jedashford/dark-moth-site/preview/board.png

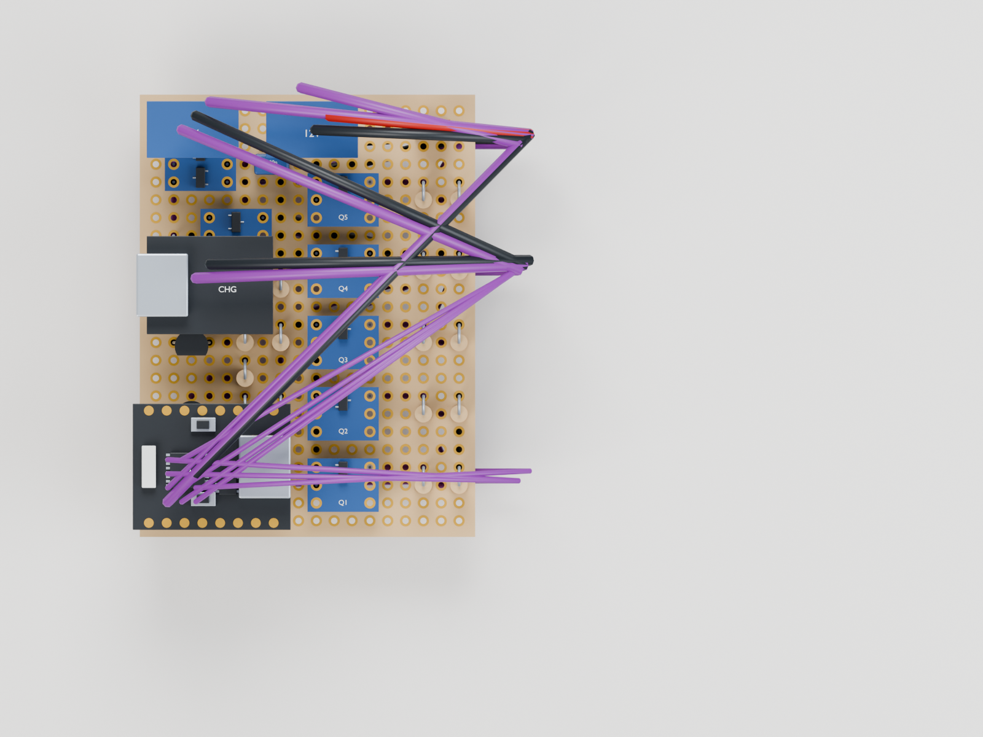
preview/board.png
