jedashford/dark-moth-site/preview/internals.png

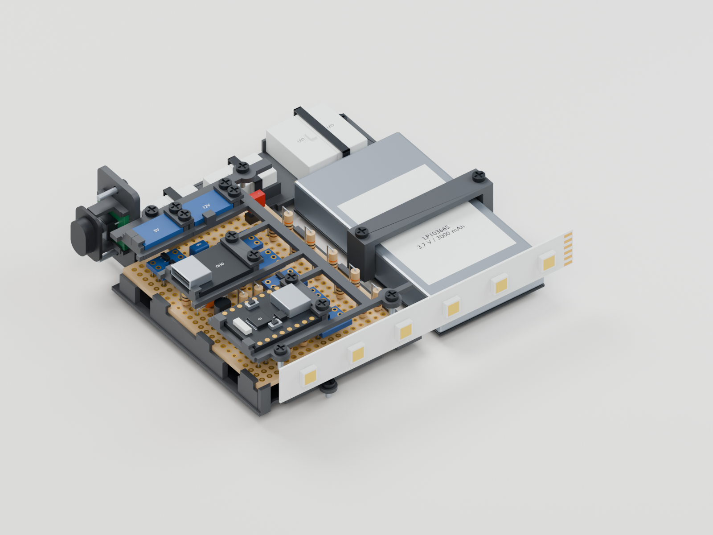
preview/internals.png
