jedashford/dark-moth-site/preview/side.png

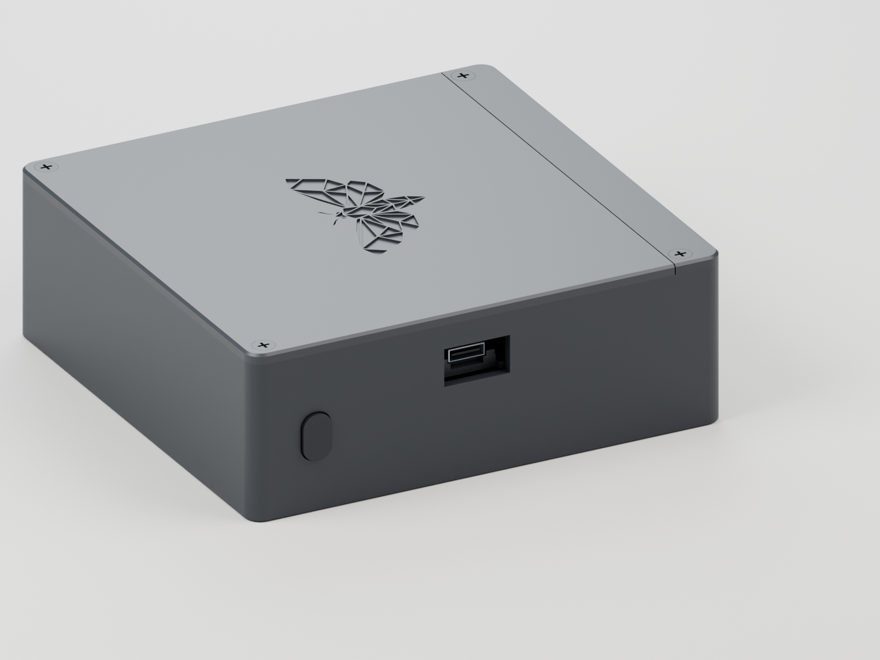
preview/side.png
