jedashford/dark-moth-site/preview/site/perfboard/carrier-angle.png

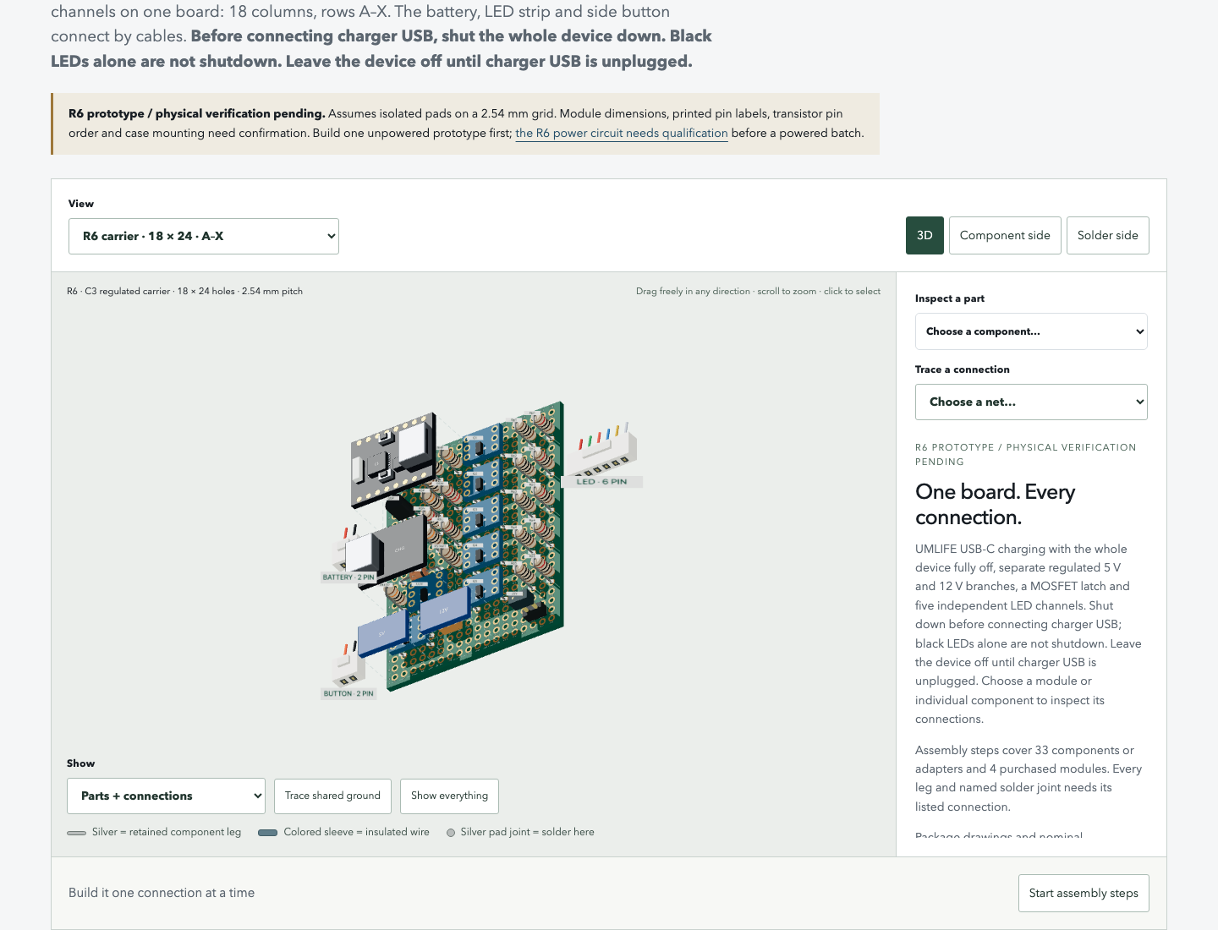
preview/site/perfboard/carrier-angle.png
