jedashford/dark-moth-site/preview/site/perfboard/carrier-bottom.png

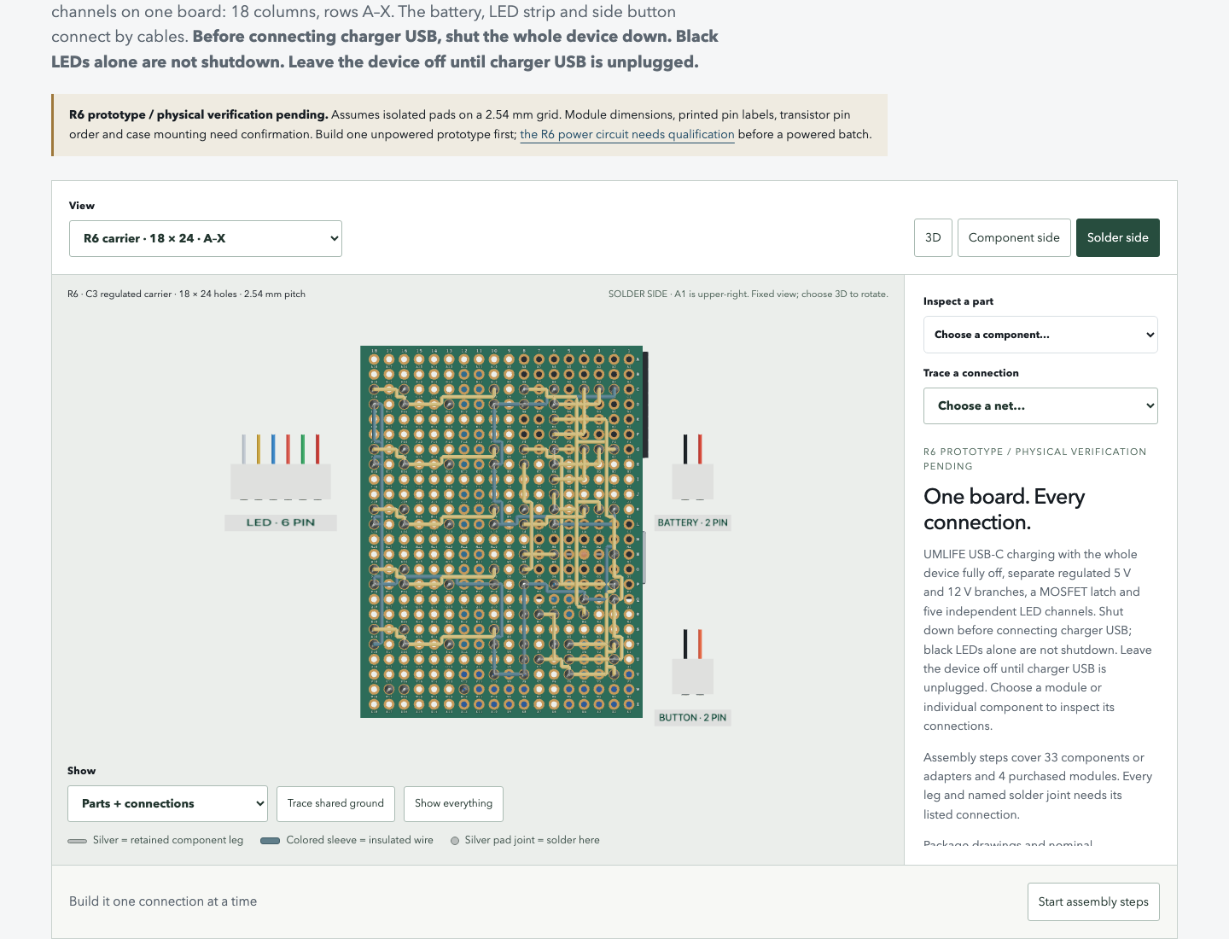
preview/site/perfboard/carrier-bottom.png
