jedashford/dark-moth-site/preview/site/perfboard/carrier-top.png

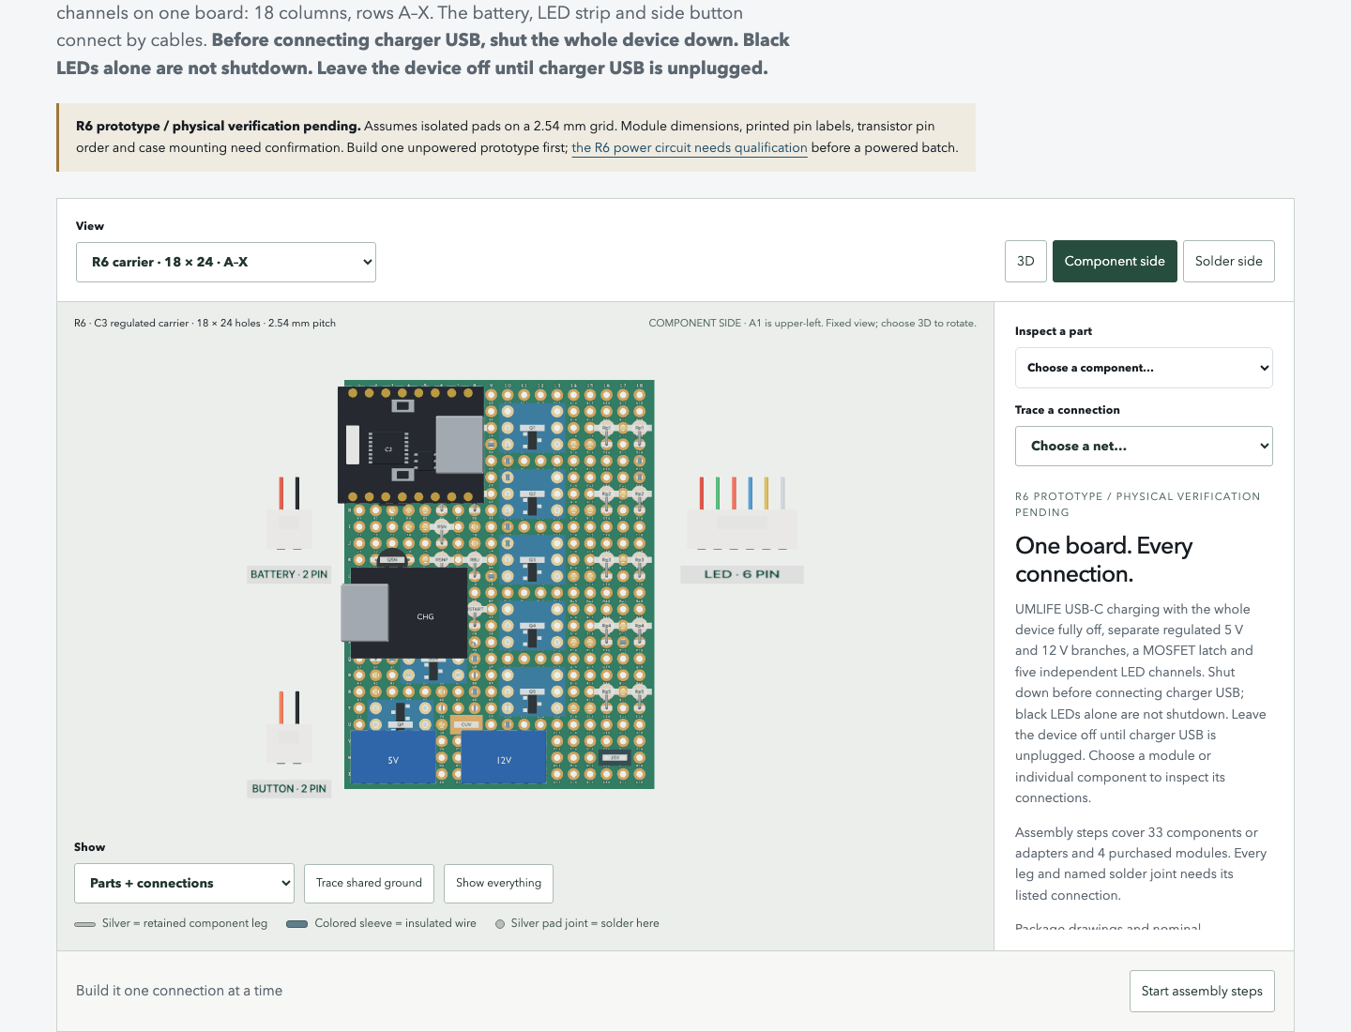
preview/site/perfboard/carrier-top.png
