jedashford/dark-moth-site/preview/site/perfboard/combined-top.png

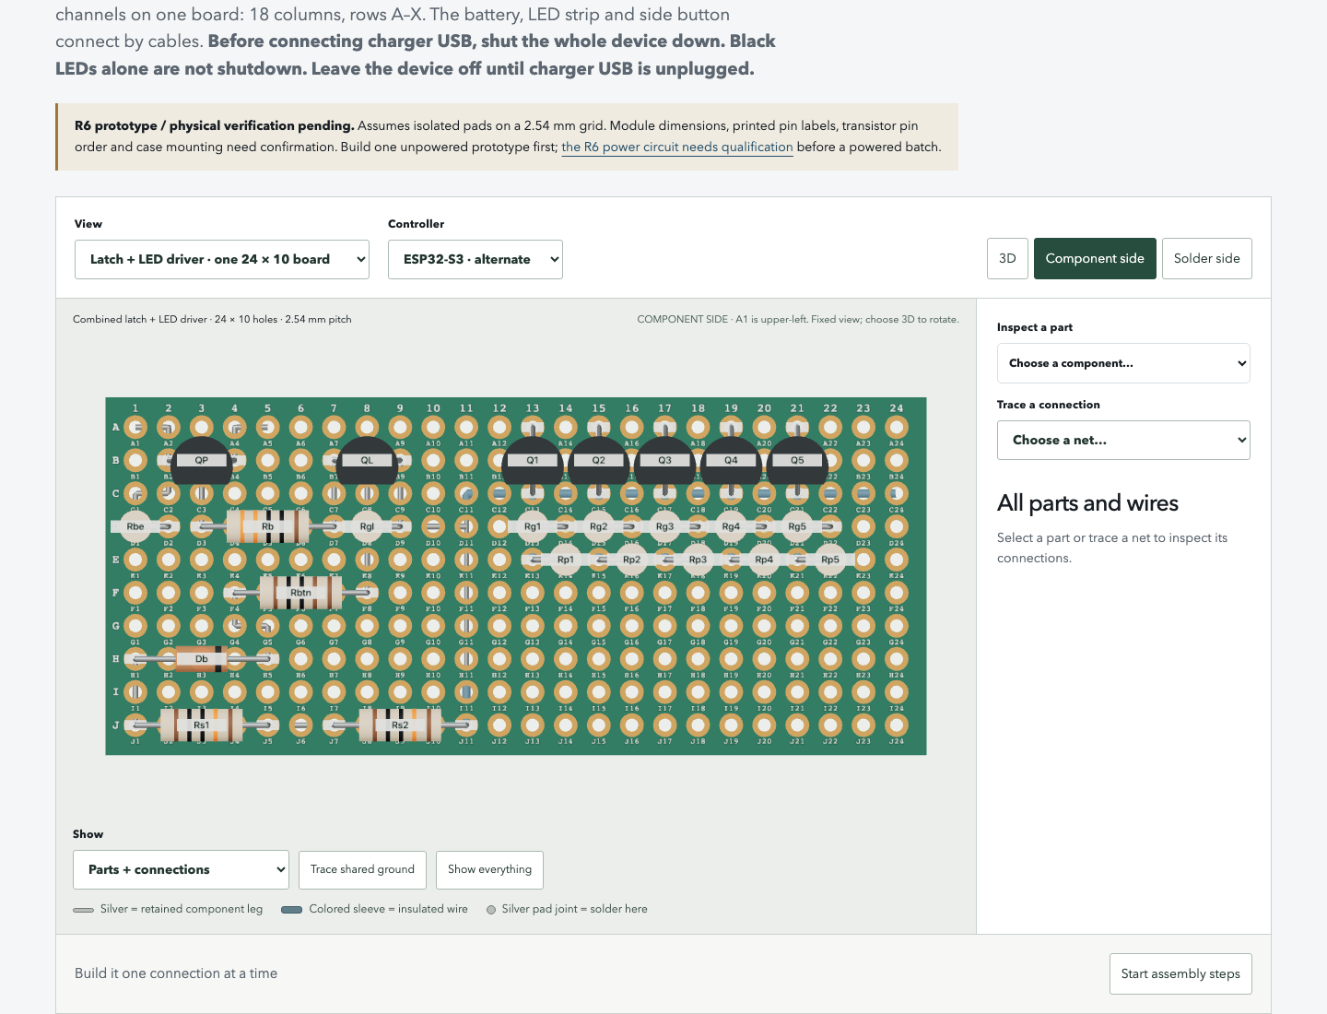
preview/site/perfboard/combined-top.png
