jedashford/dark-moth-site/preview/site/perfboard/controller.png

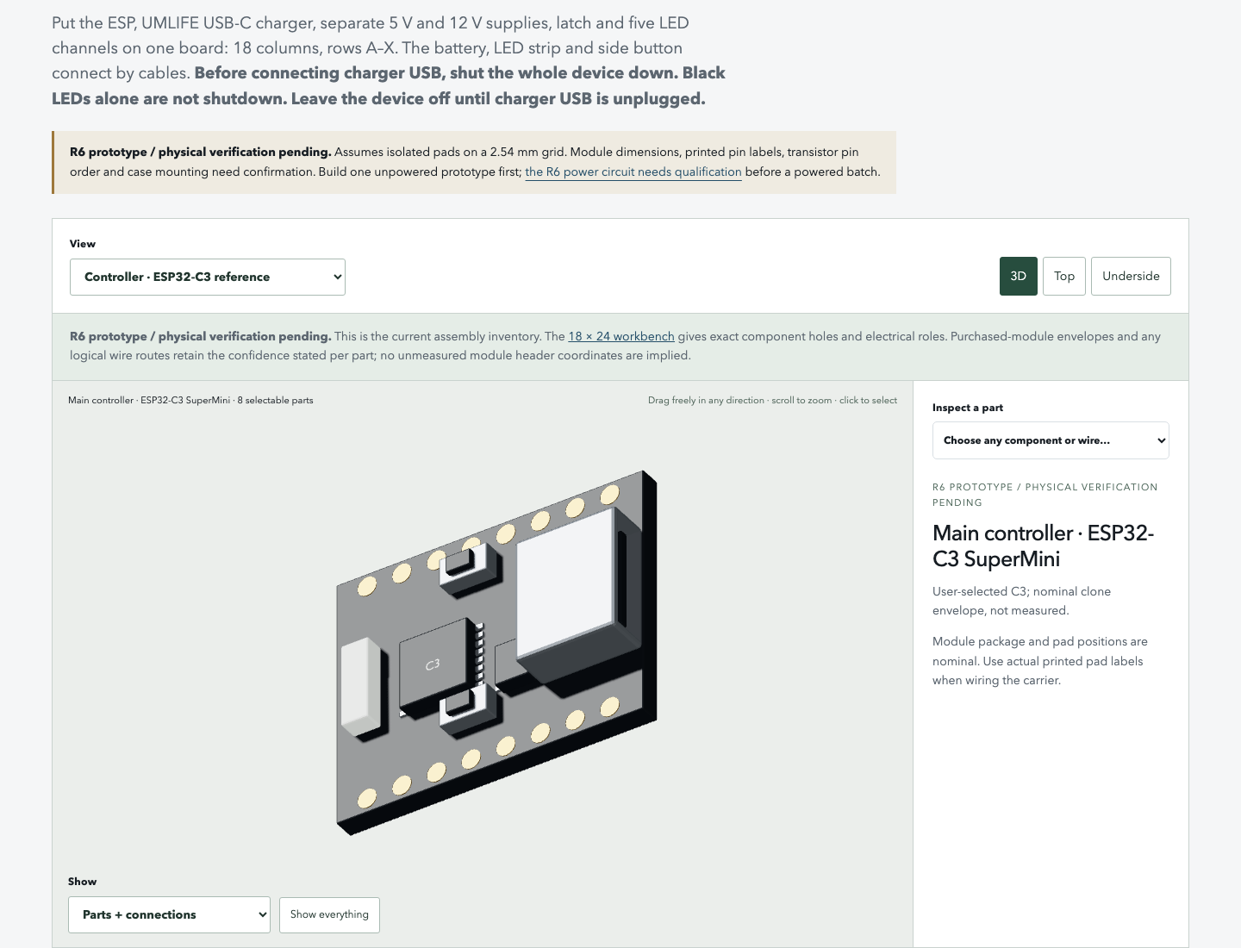
preview/site/perfboard/controller.png
