jedashford/dark-moth-site/preview/site/perfboard/driver-3d.png

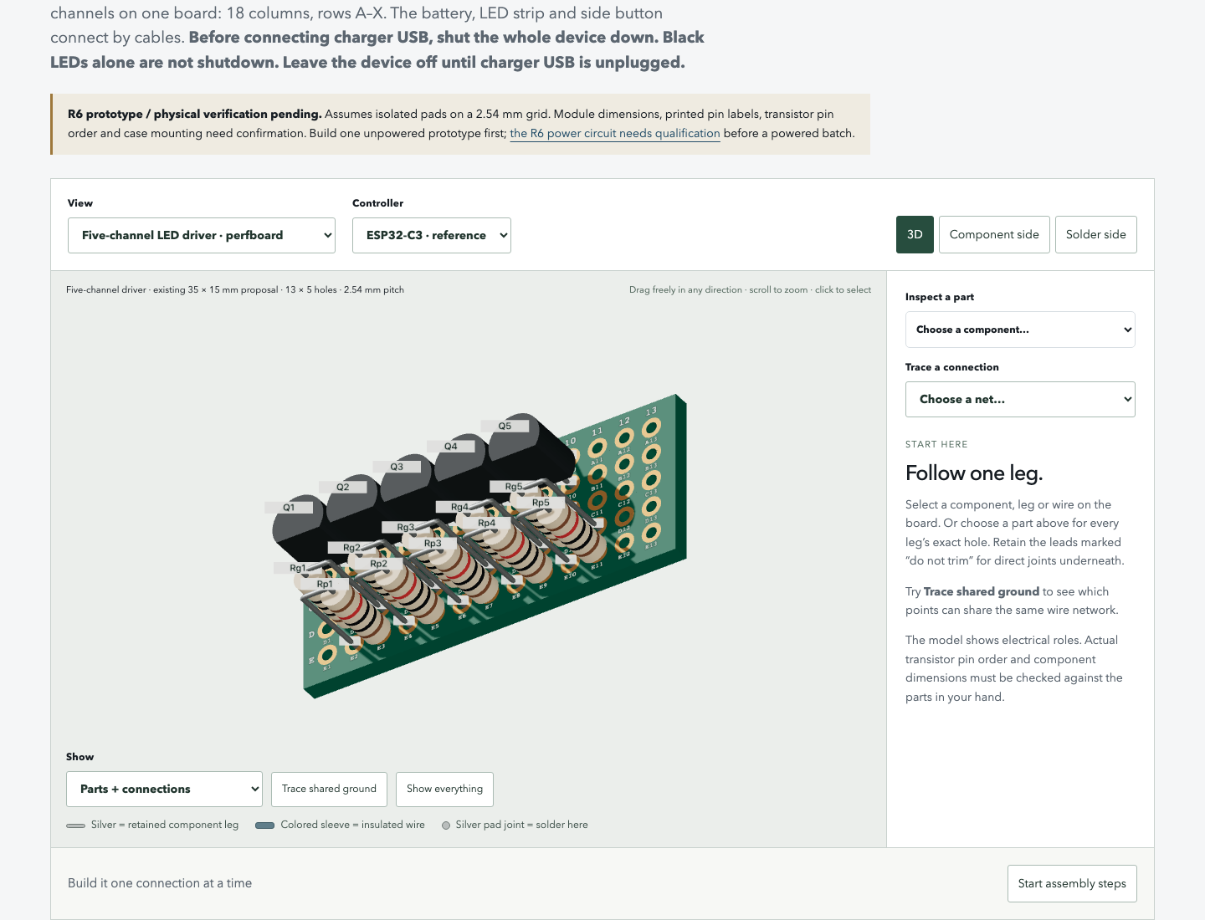
preview/site/perfboard/driver-3d.png
