jedashford/dark-moth-site/preview/site/perfboard/driver-ground-bottom.png

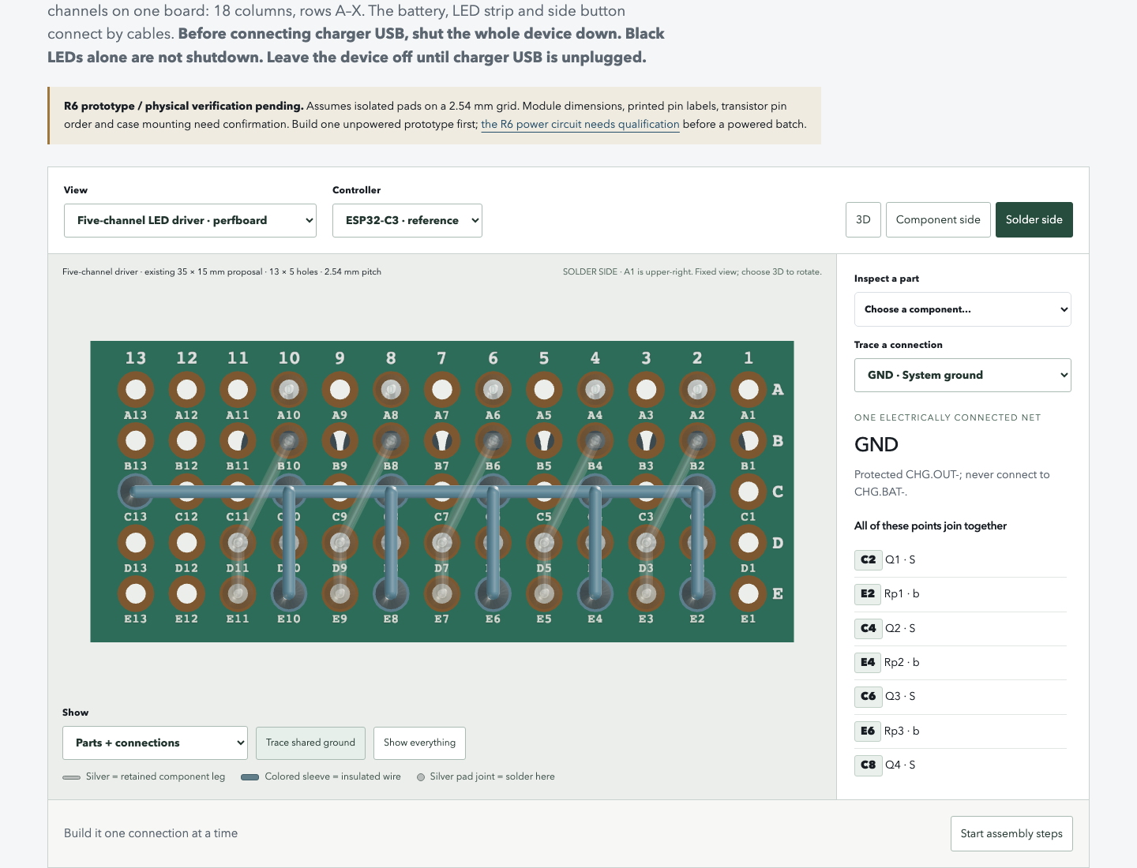
preview/site/perfboard/driver-ground-bottom.png
