jedashford/dark-moth-site/preview/site/perfboard/latch-ground-bottom.png

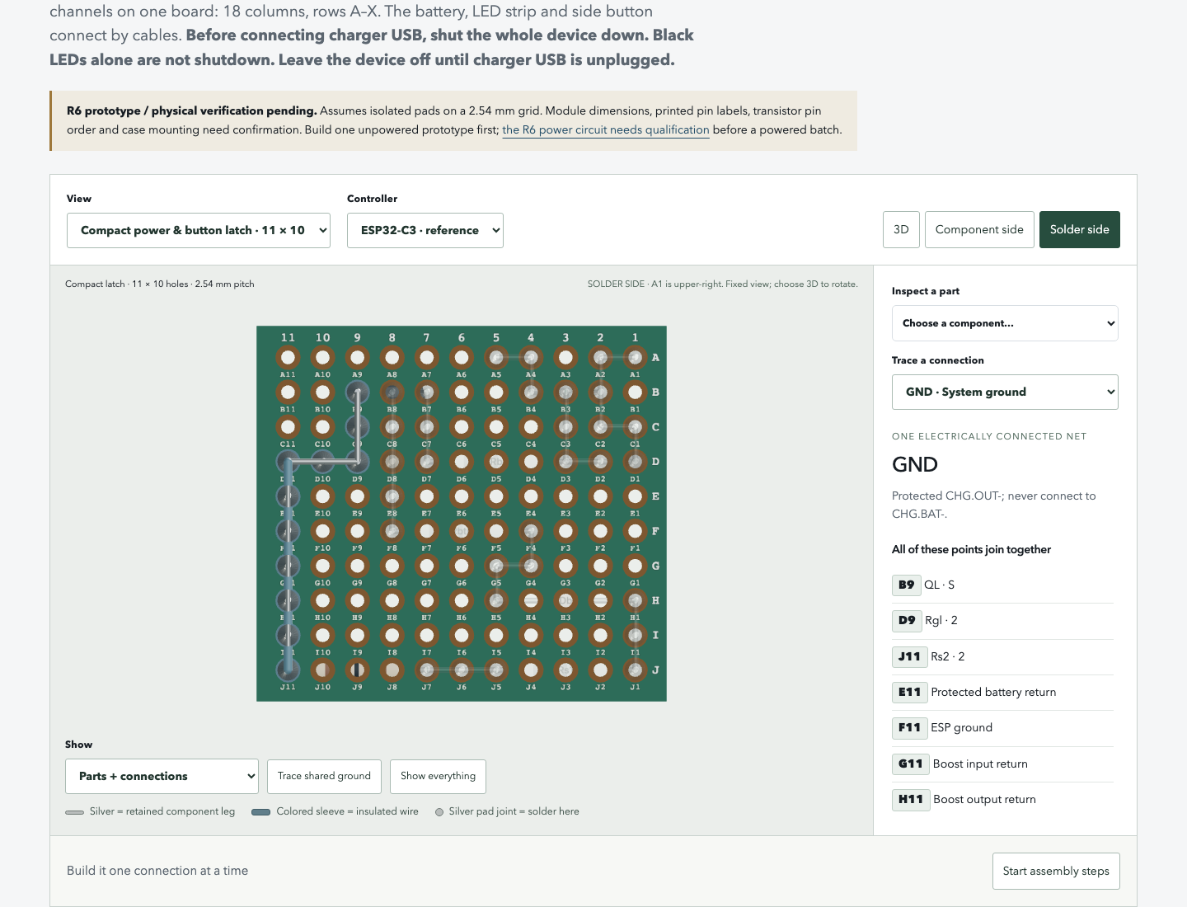
preview/site/perfboard/latch-ground-bottom.png
