jedashford/dark-moth-site/preview/site/perfboard/latch-top.png

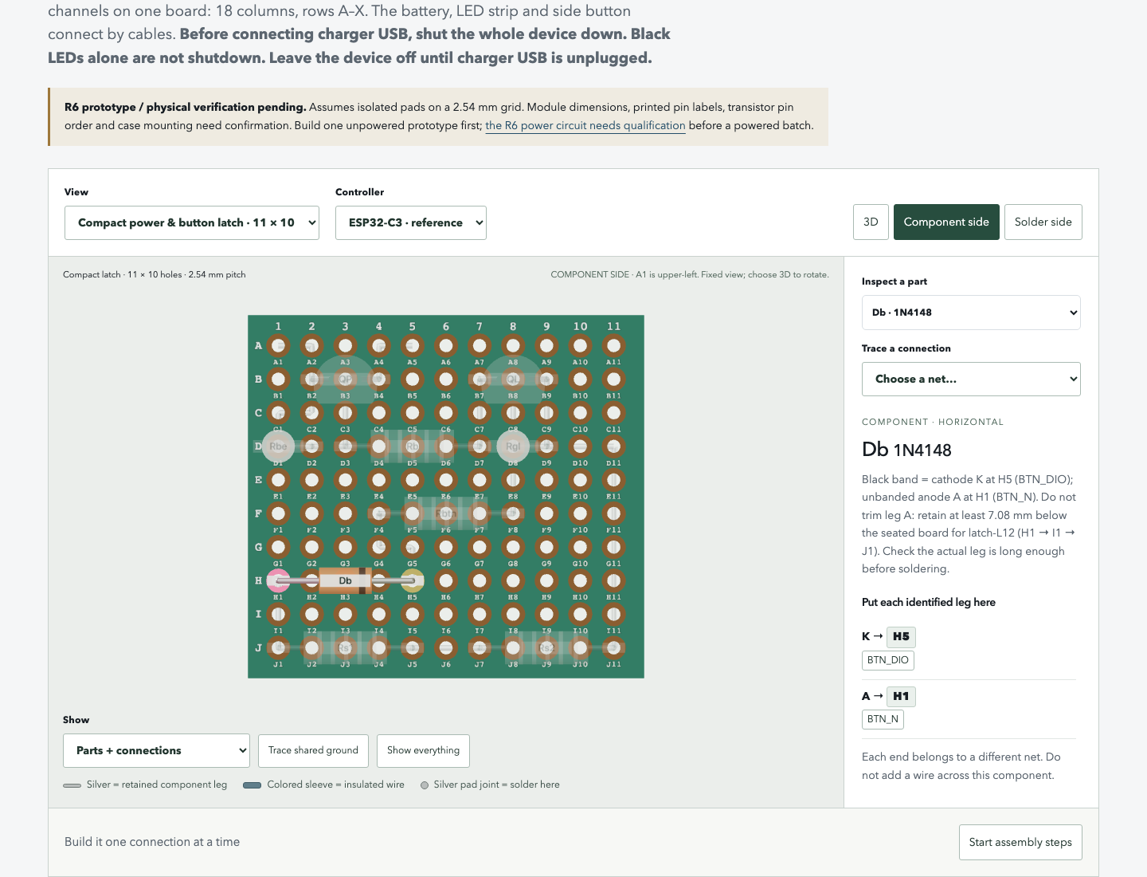
preview/site/perfboard/latch-top.png
