jedashford/dark-moth-site/preview/site/perfboard/main-pcb.png

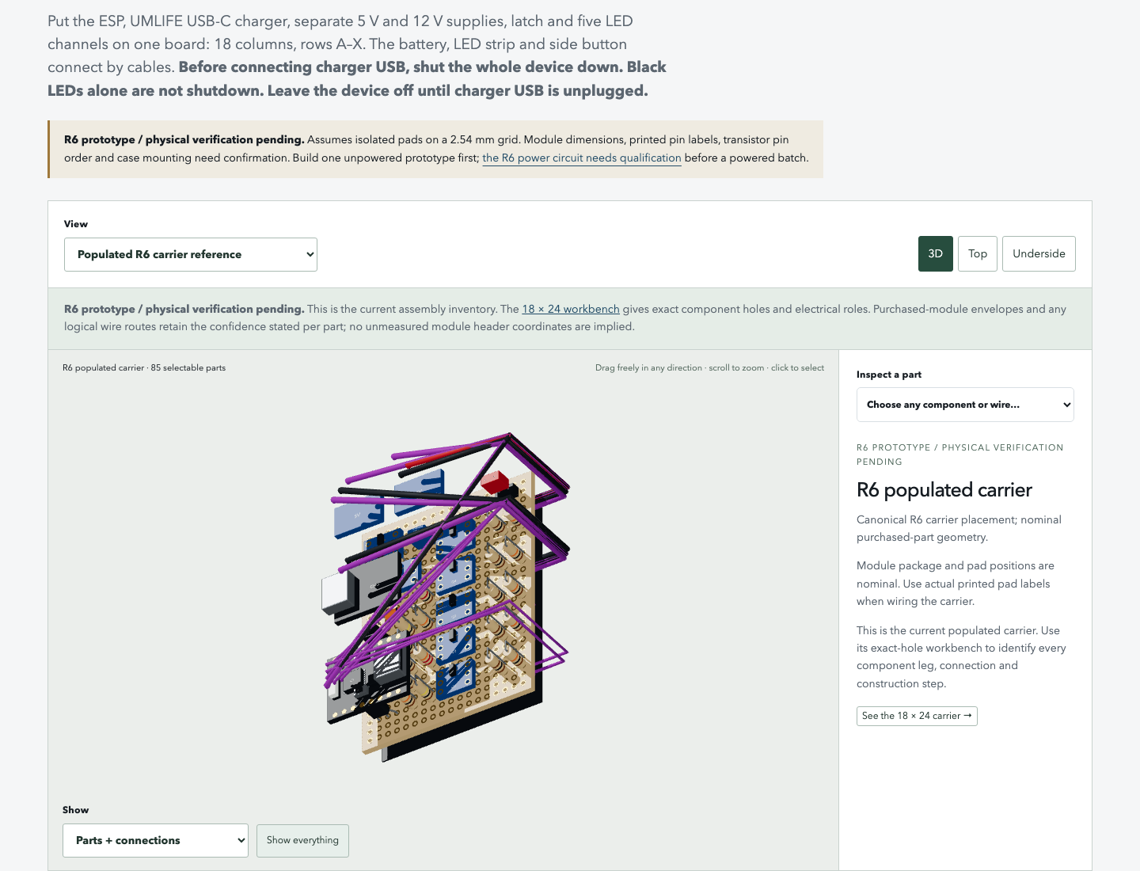
preview/site/perfboard/main-pcb.png
