jedashford/dark-moth-site/preview/site/perfboard/mobile.png

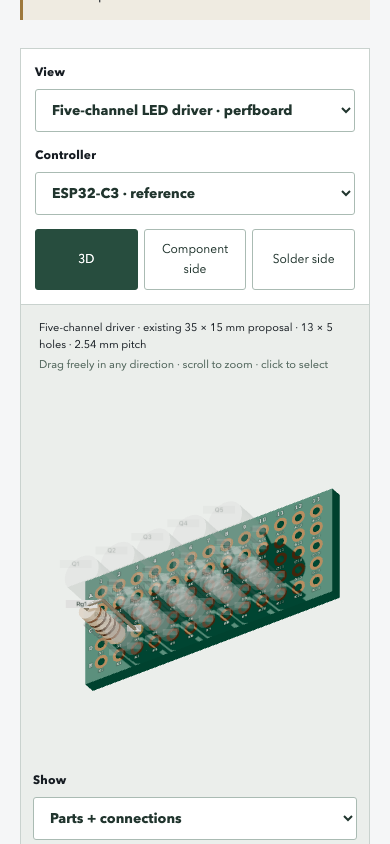
preview/site/perfboard/mobile.png
