jedashford/dark-moth-site/preview/site/perfboard/navigation.png

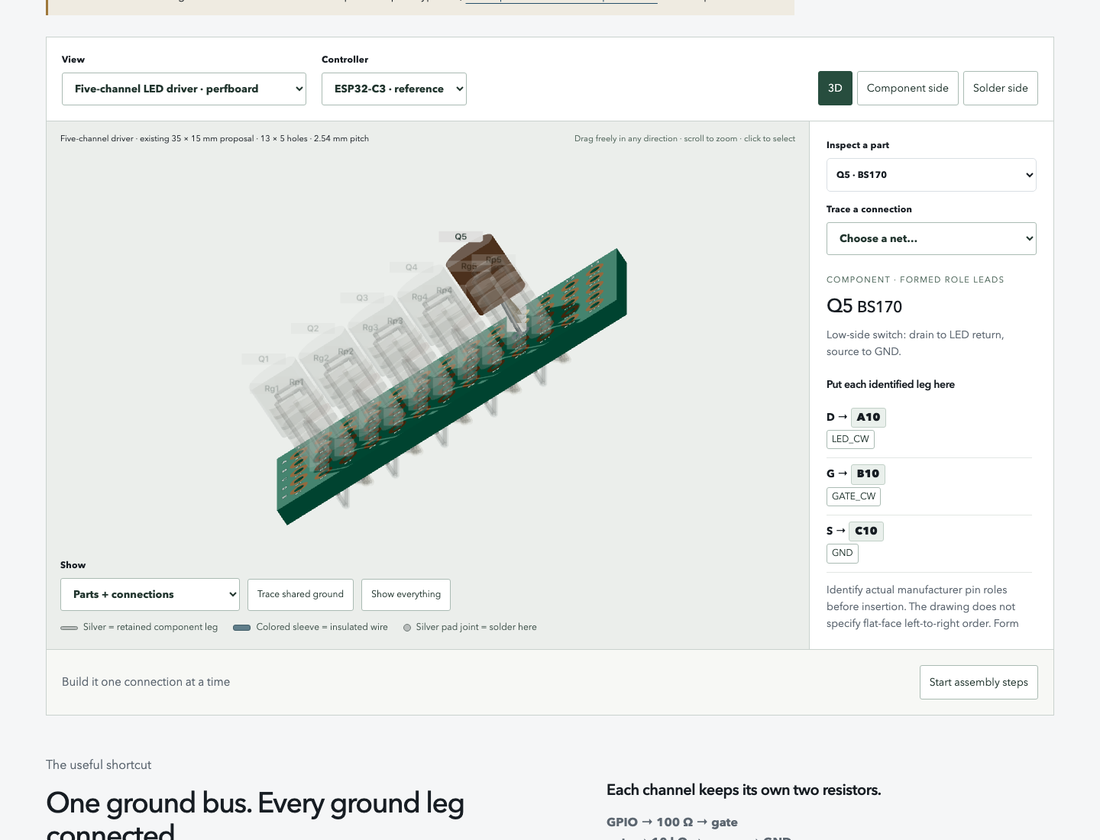
preview/site/perfboard/navigation.png
