jedashford/dark-moth-site/preview/site/r6/diffuser-access.png

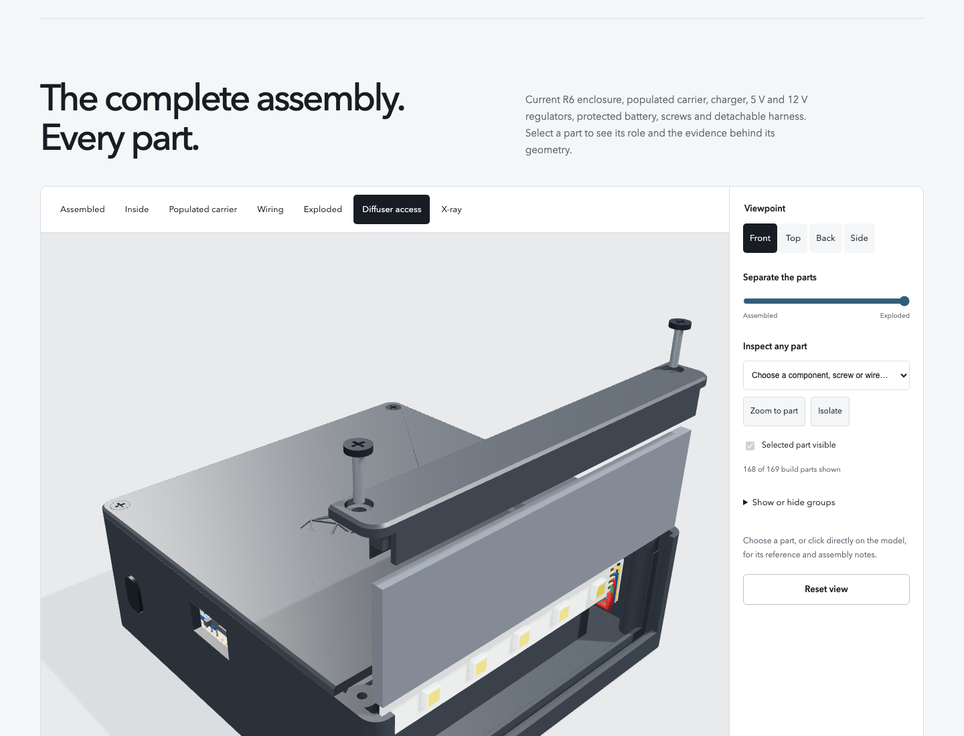
preview/site/r6/diffuser-access.png
