jedashford/dark-moth-site/preview/site/r6/mobile.png

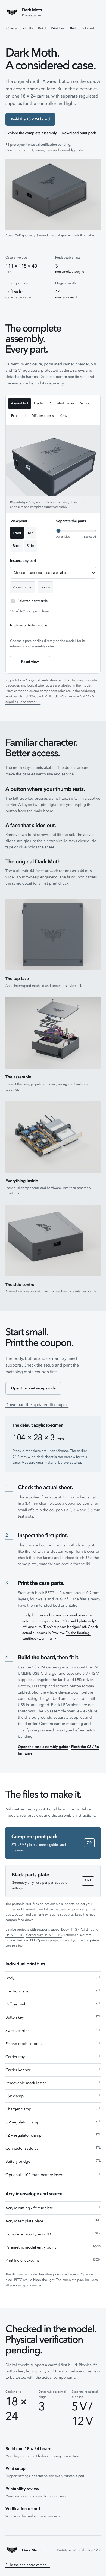
preview/site/r6/mobile.png
