jedashford/dark-moth-site/preview/top.png

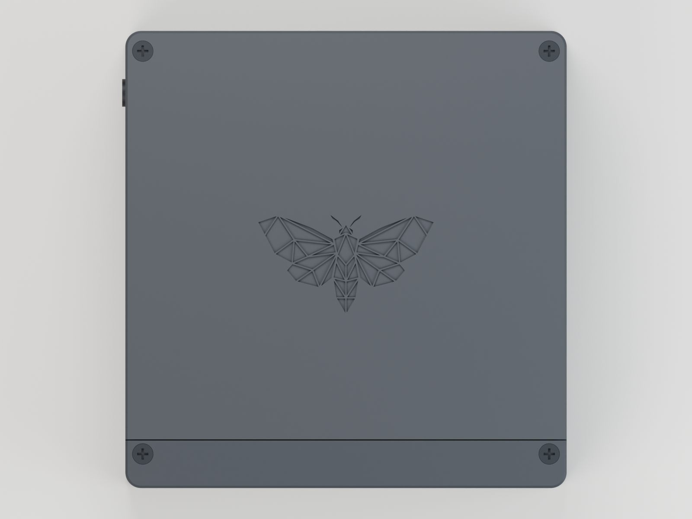
preview/top.png
