jedashford/dark-moth-site/prints/clamp_esp.stl

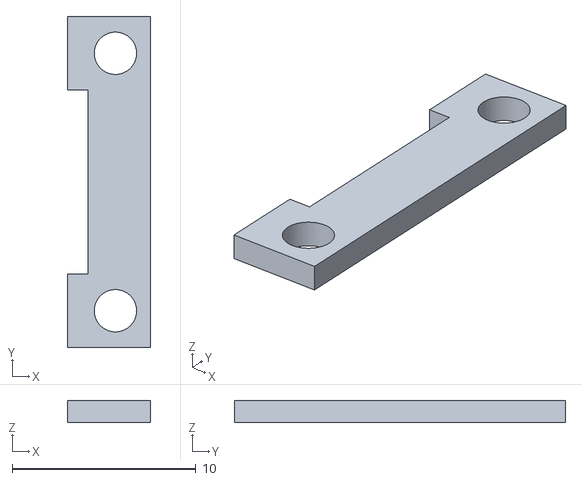
[picture p40: CAD file, 2026-09-19]
prints/clamp_esp.stl
4.50 x 18.0 x 1.20
