jedashford/dark-moth-site/prints/coupon.stl

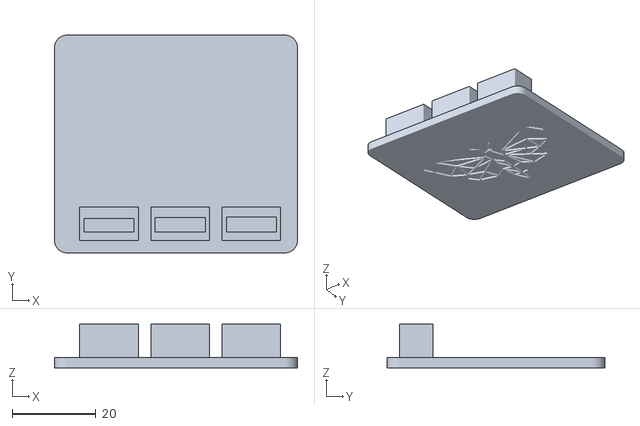
[picture p41: CAD file, 2026-09-13]
prints/coupon.stl
58.0 x 52.0 x 10.4
