jedashford/dark-moth-site/prints/switch_carrier.stl

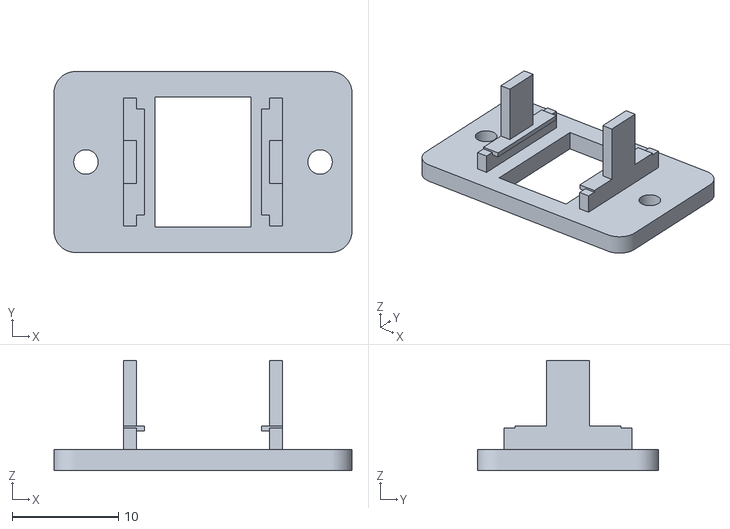
[picture p42: CAD file, 2026-09-13]
prints/switch_carrier.stl
28.0 x 17.0 x 10.4
