jedashford/dark-moth-site/preview/site/r6/board-guide.png

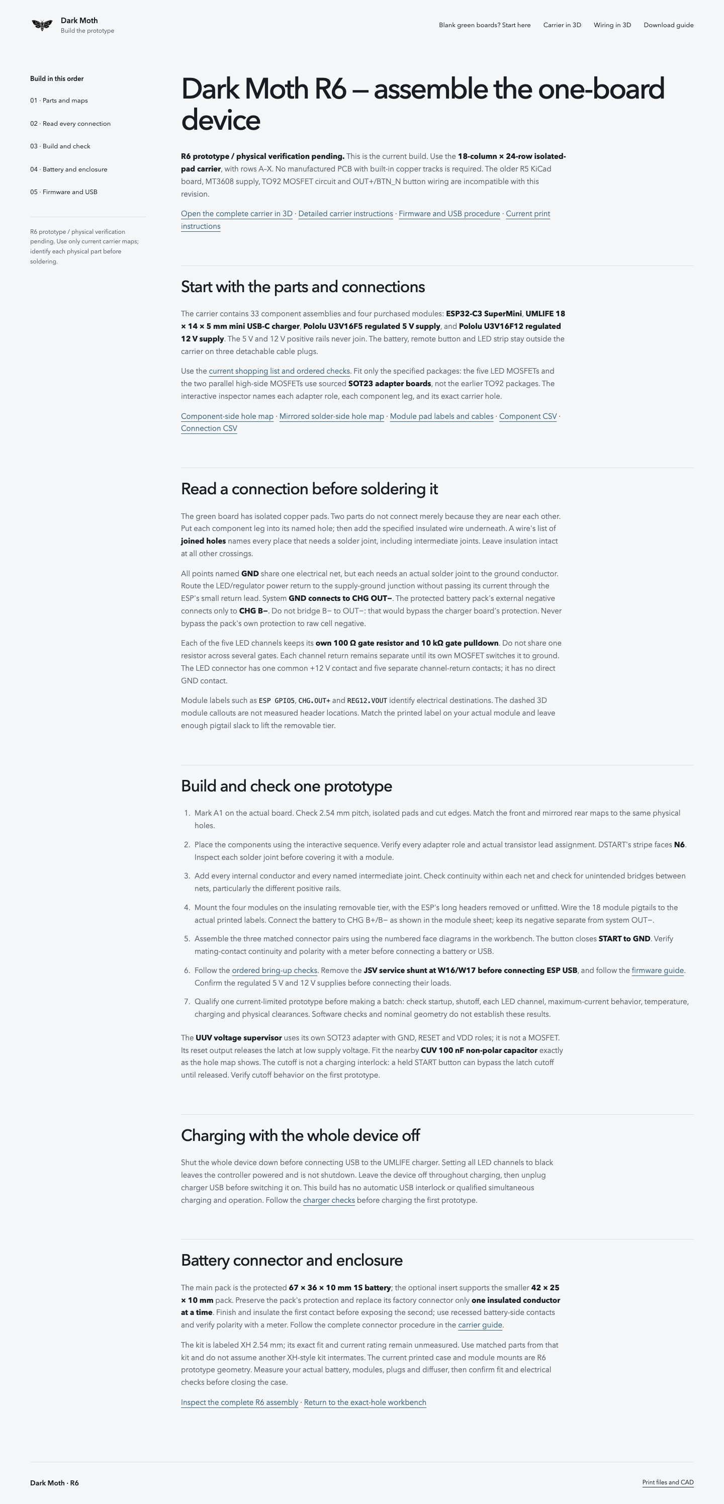
preview/site/r6/board-guide.png
