jedashford/dark-moth-site/preview/site/r6/print-downloads.png

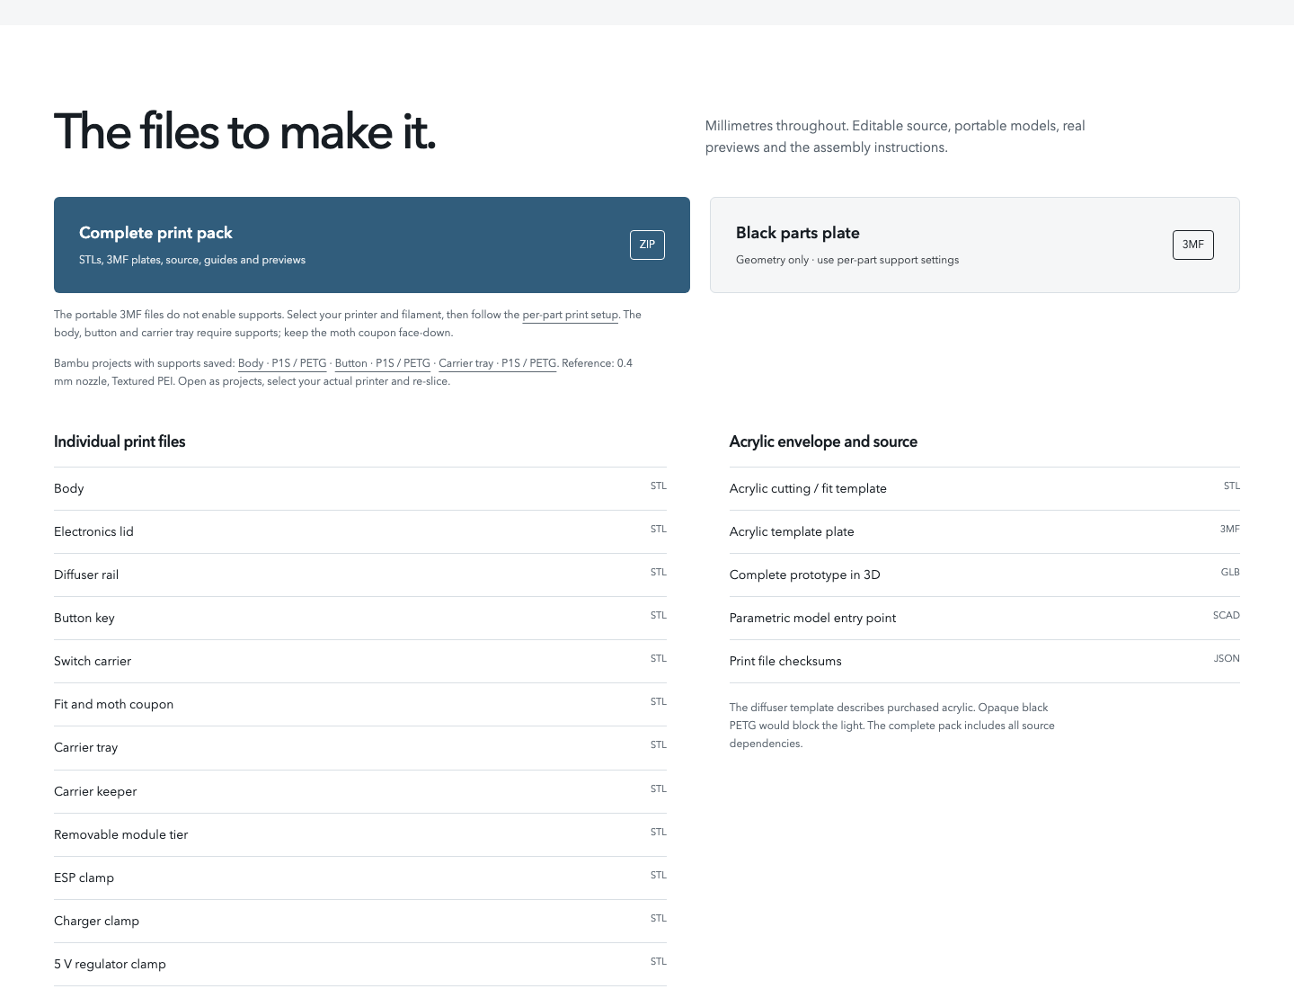
preview/site/r6/print-downloads.png
