jedashford/dark-moth-site/preview/site/r6/print-guide.png

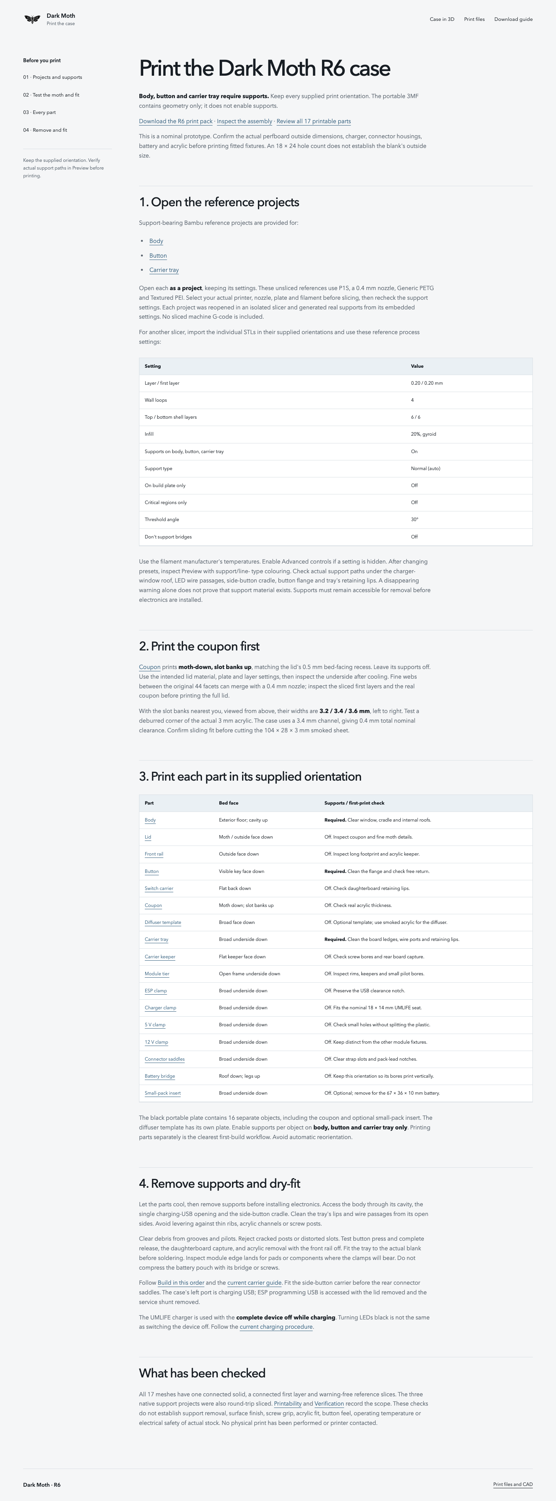
preview/site/r6/print-guide.png
