jedashford/dark-moth-site/preview/site/r6/print-mobile.png

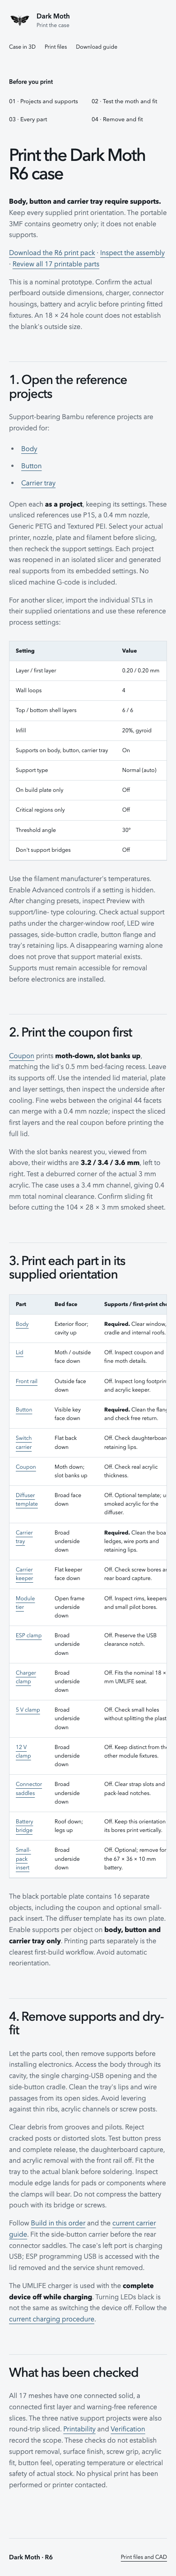
preview/site/r6/print-mobile.png
